danielstoller/ECE-1895-Bop-it/Enclosure/pictures/empty_enclosure_back.JPG

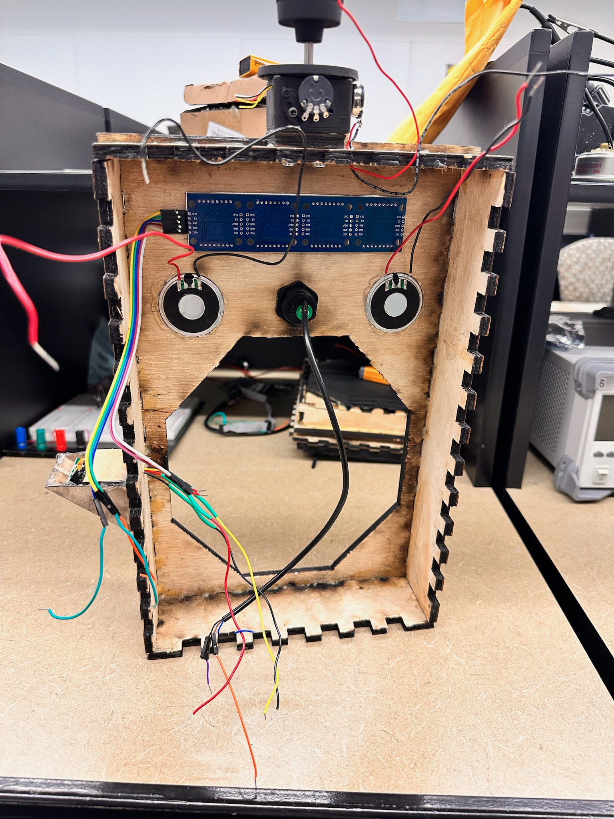
Enclosure/pictures/empty_enclosure_back.JPG
