danielstoller/ECE-1895-Bop-it/Enclosure/pictures/empty_enclosure_front.JPG

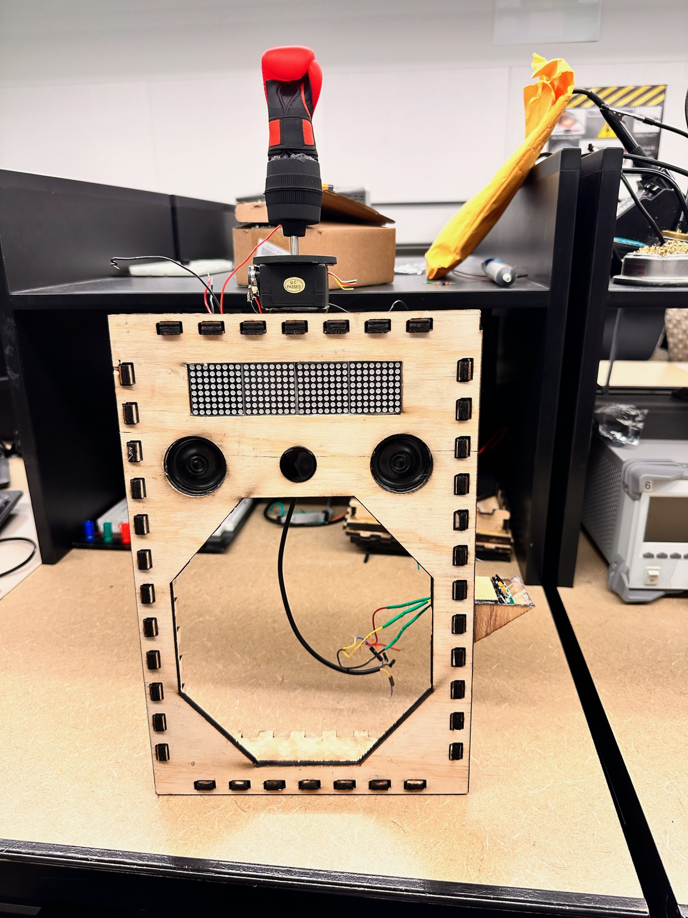
Enclosure/pictures/empty_enclosure_front.JPG
