danielstoller/ECE-1895-Bop-it/Enclosure/pictures/empty_enclosure_front_2.JPG

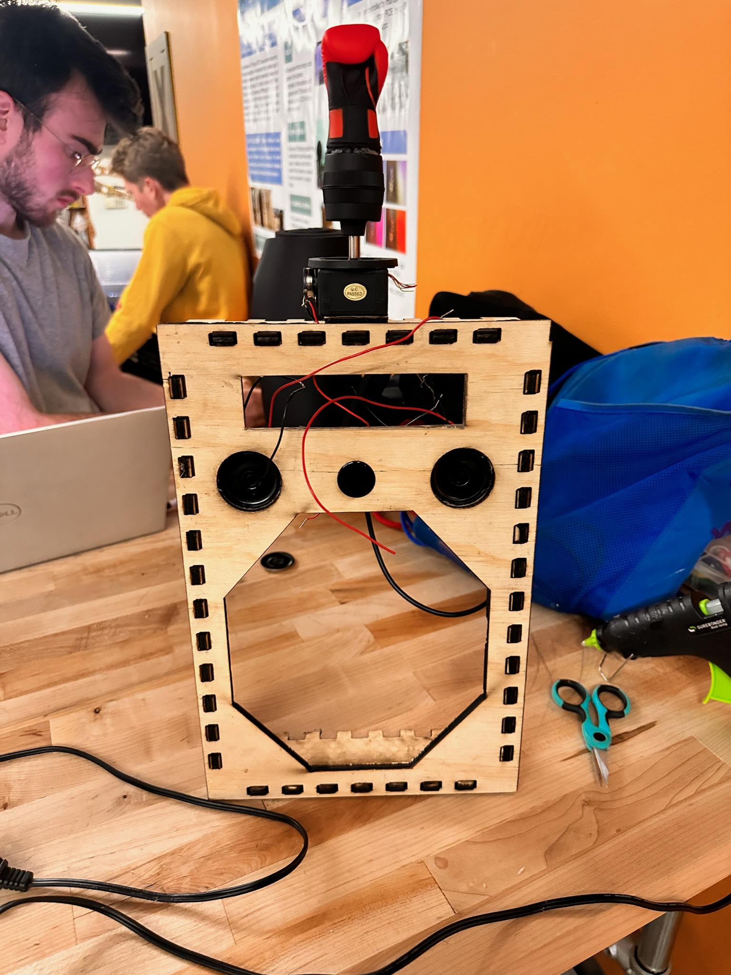
Enclosure/pictures/empty_enclosure_front_2.JPG
