danielstoller/ECE-1895-Bop-it/Enclosure/pictures/enclosure_front.JPG

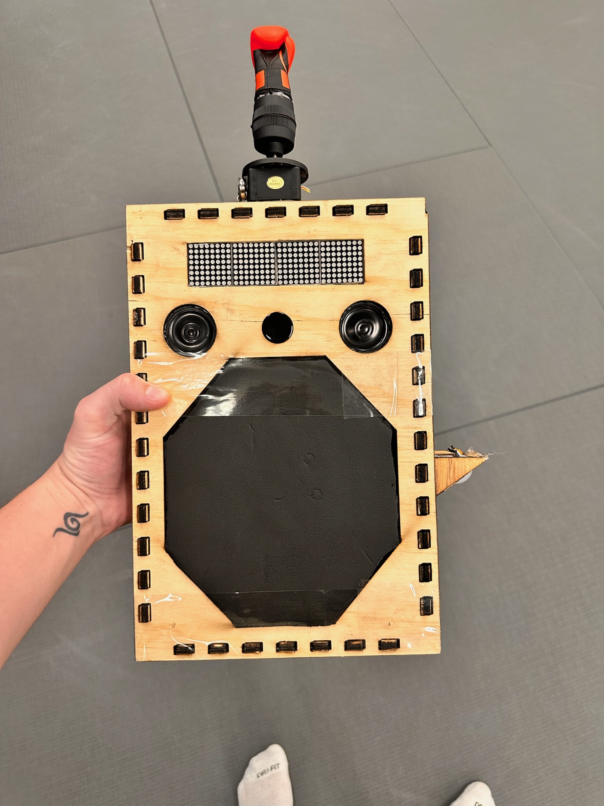
Enclosure/pictures/enclosure_front.JPG
