danielstoller/ECE-1895-Bop-it/Enclosure/pictures/enclosure_front_2.JPG

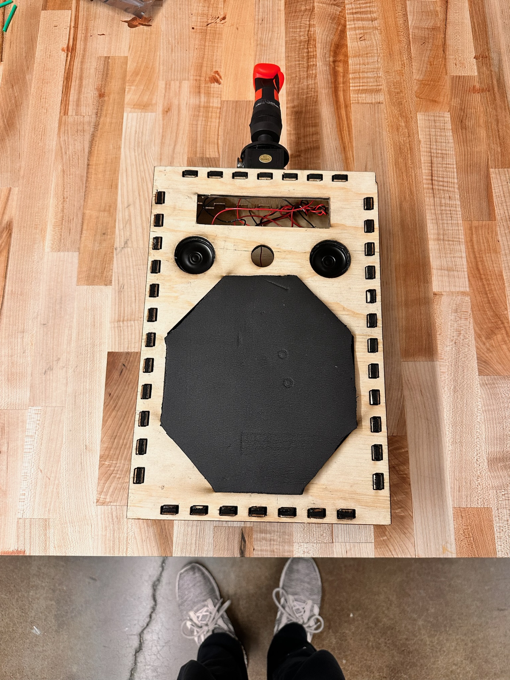
Enclosure/pictures/enclosure_front_2.JPG
