danielstoller/ECE-1895-Bop-it/Enclosure/pictures/enclosure_front_back.png

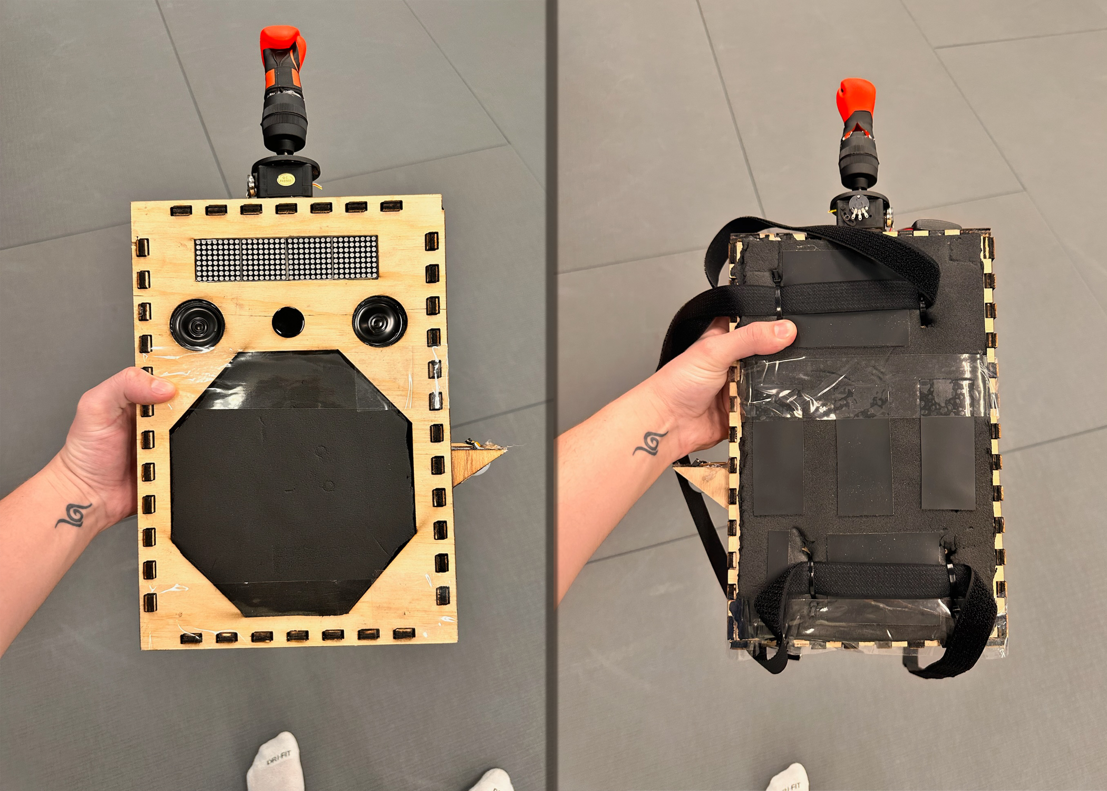
Enclosure/pictures/enclosure_front_back.png
