danielstoller/ECE-1895-Bop-it/Enclosure/pictures/enclosure_model.PNG

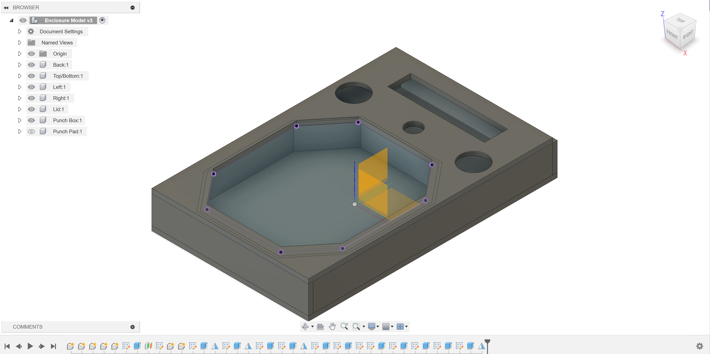
Enclosure/pictures/enclosure_model.PNG
