danielstoller/ECE-1895-Bop-it/Enclosure/pictures/enclosure_model_no_lid.PNG

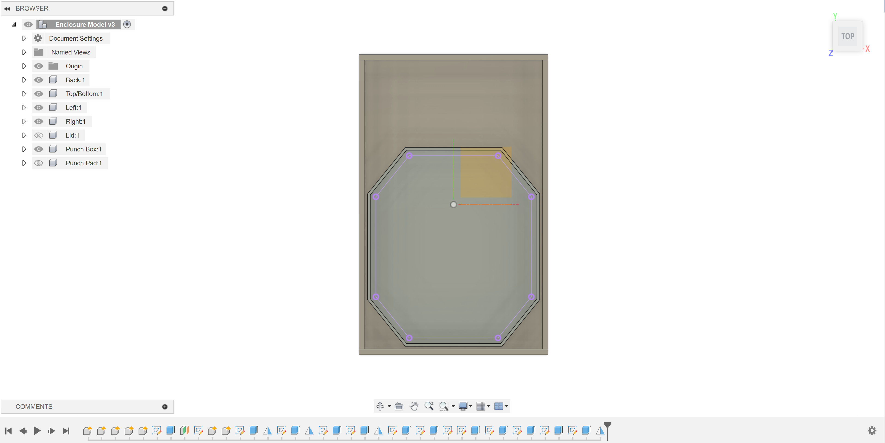
Enclosure/pictures/enclosure_model_no_lid.PNG
