danielstoller/ECE-1895-Bop-it/Enclosure/pictures/enclosure_no_lid.JPG

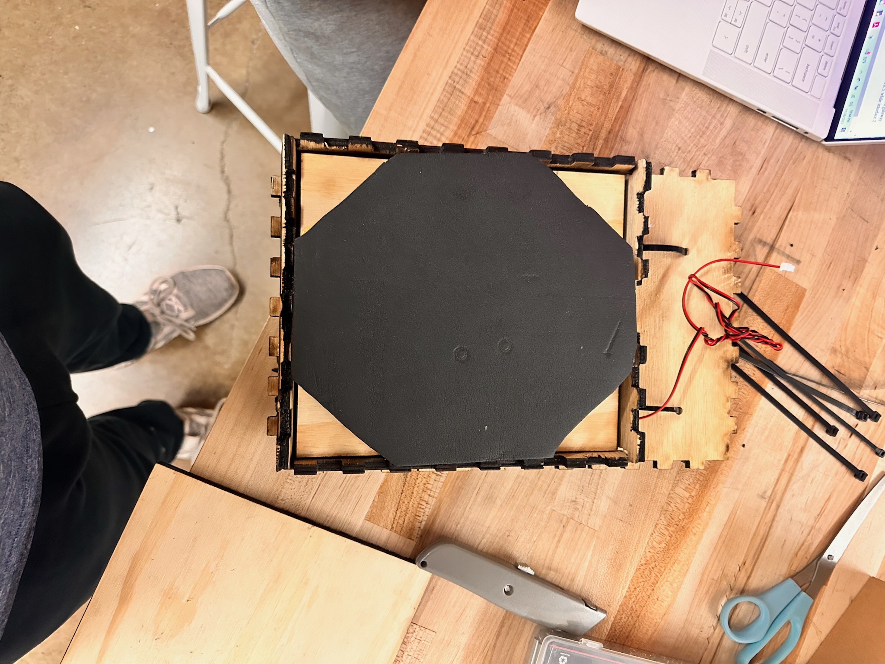
Enclosure/pictures/enclosure_no_lid.JPG
