danielstoller/ECE-1895-Bop-it/Enclosure/pictures/IMG_3901.JPG

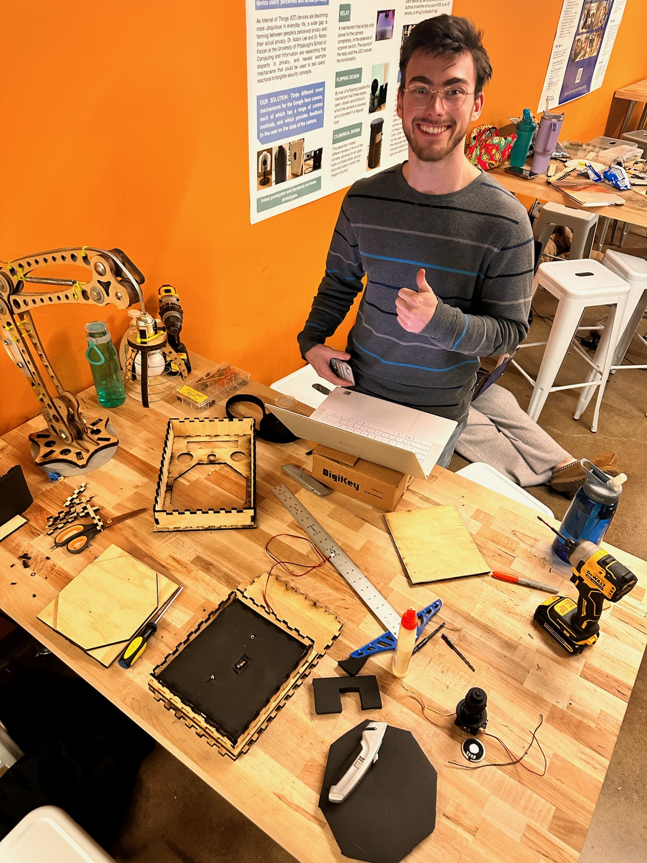
Enclosure/pictures/IMG_3901.JPG
