danielstoller/ECE-1895-Bop-it/Enclosure/pictures/separated_enclosure.JPG

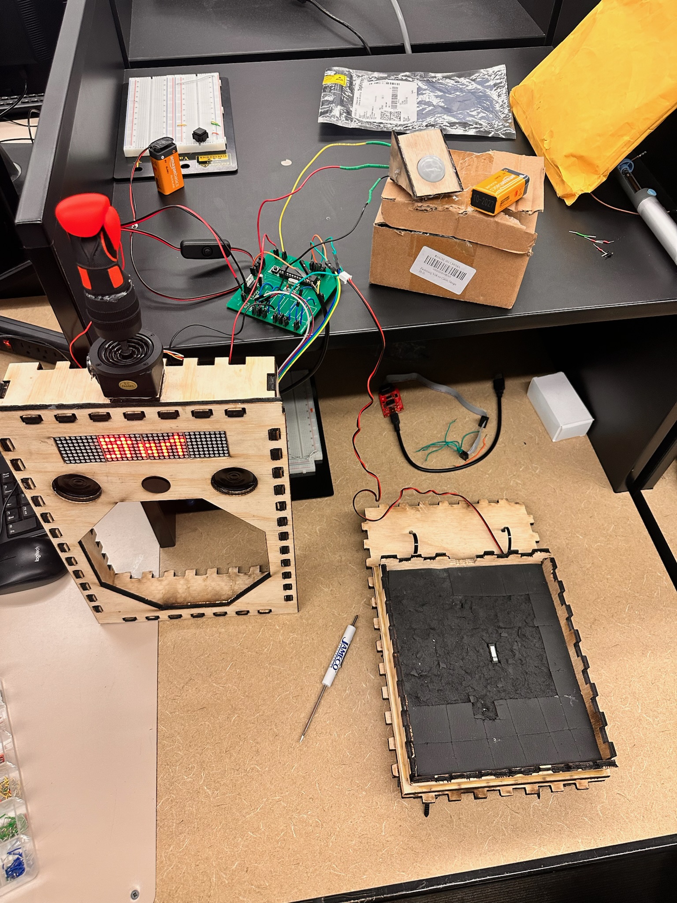
Enclosure/pictures/separated_enclosure.JPG
