danielstoller/ECE-1895-Bop-it/Pictures/IMG_3498.JPG

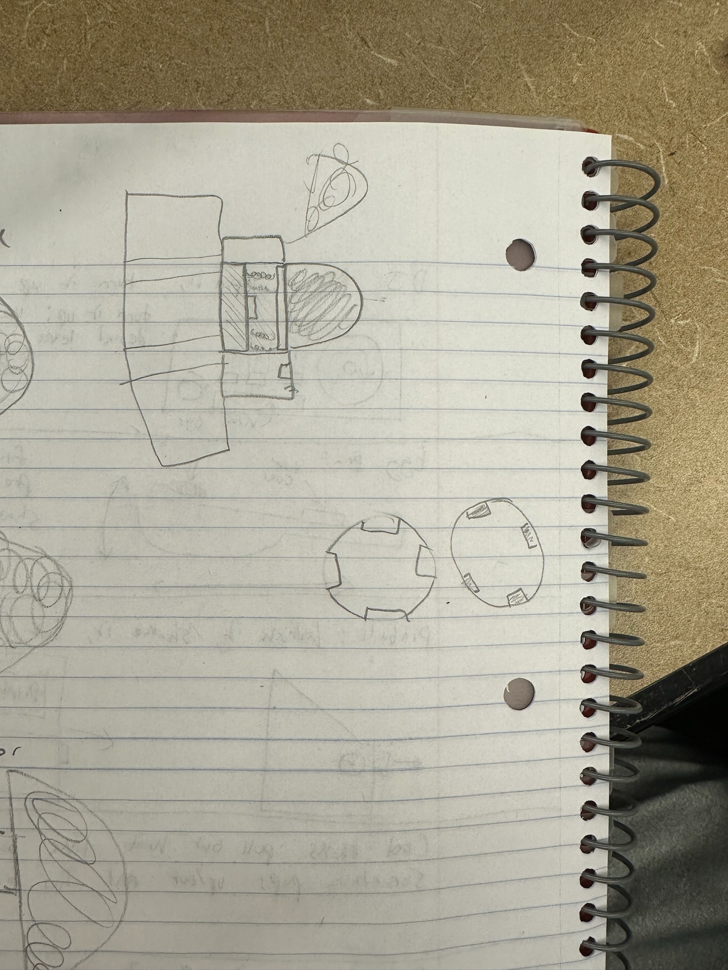
Pictures/IMG_3498.JPG
