danielstoller/ECE-1895-Bop-it/Pictures/IMG_3929.JPG

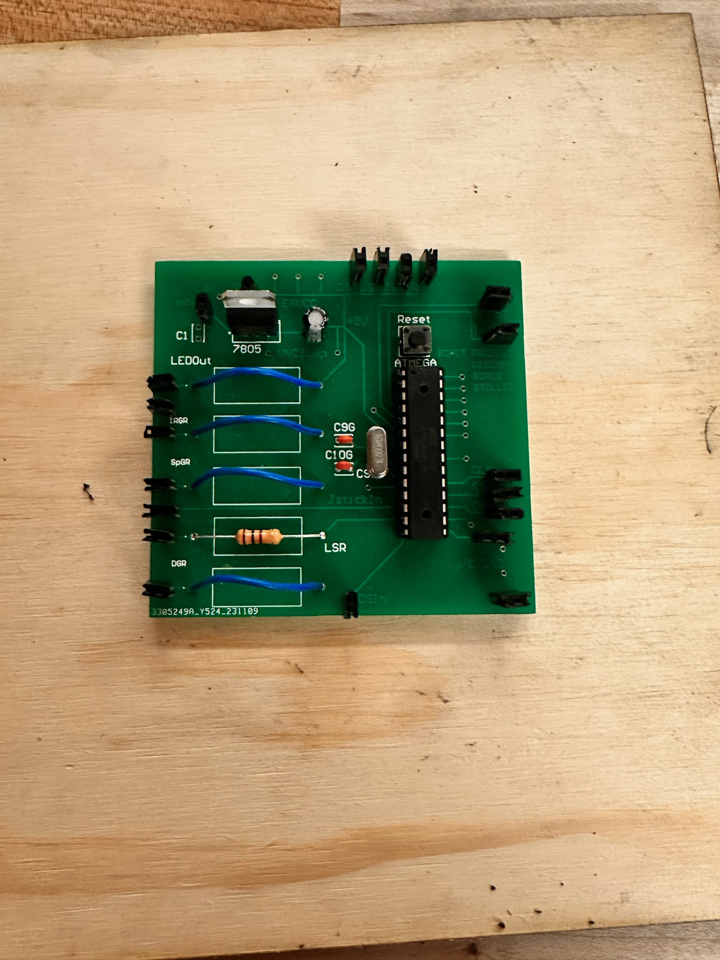
Pictures/IMG_3929.JPG
