danielstoller/ECE-1895-Bop-it/Pictures/IMG_3951.JPG

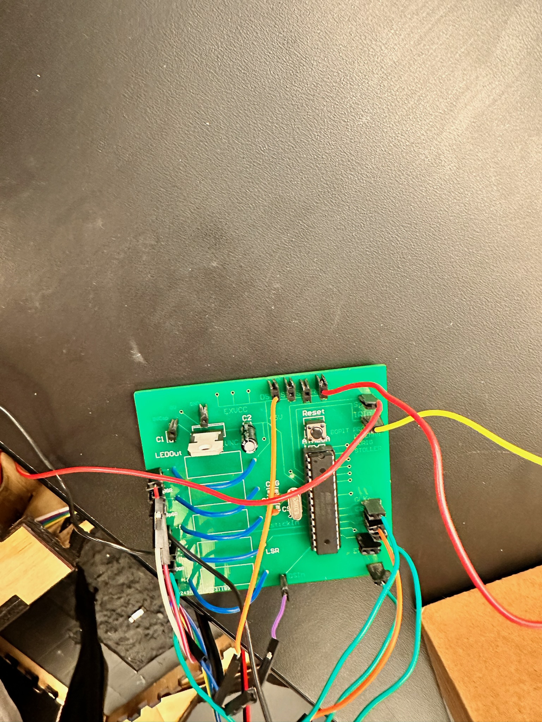
Pictures/IMG_3951.JPG
