danielstoller/ECE-1895-Bop-it/Pictures/IMG_3952.JPG

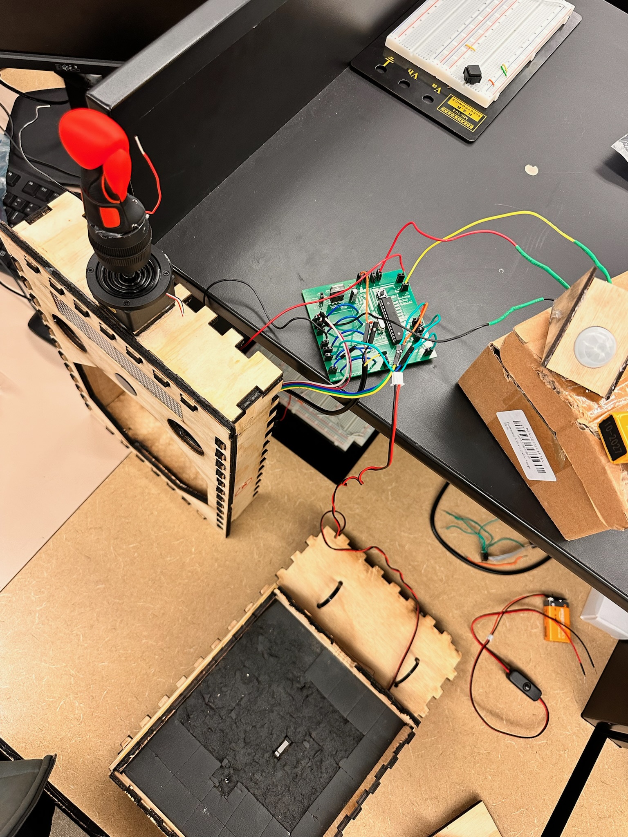
Pictures/IMG_3952.JPG
