danielstoller/ECE-1895-Bop-it/Pictures/IMG_3953.JPG

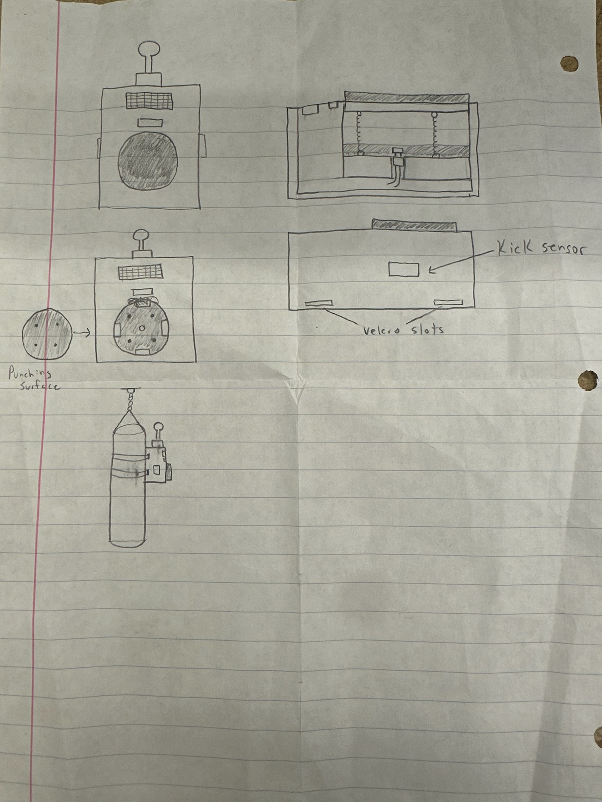
Pictures/IMG_3953.JPG
