danielstoller/ECE-1895-Bop-it/Pictures/IMG_8195.JPG

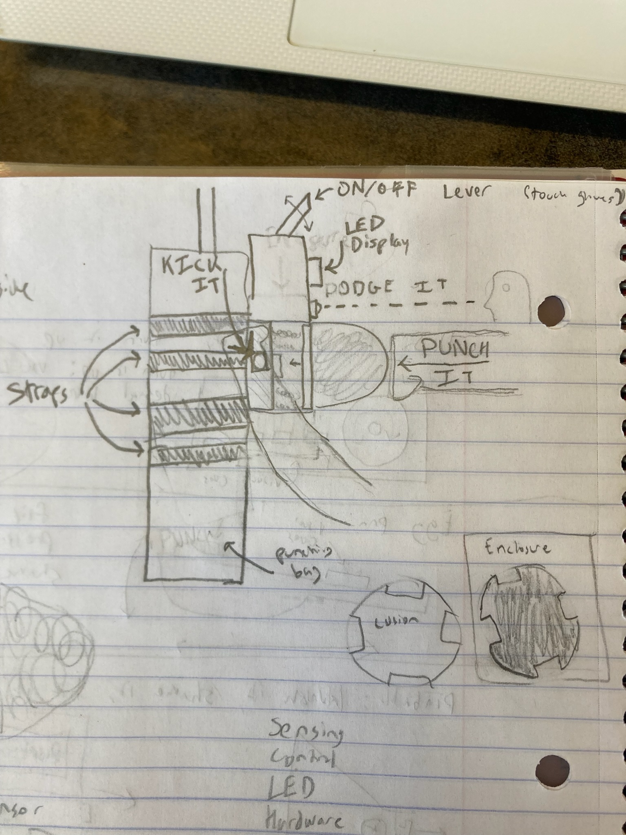
Pictures/IMG_8195.JPG
