danielstoller/ECE-1895-Bop-it/Pictures/IMG_8196.JPG

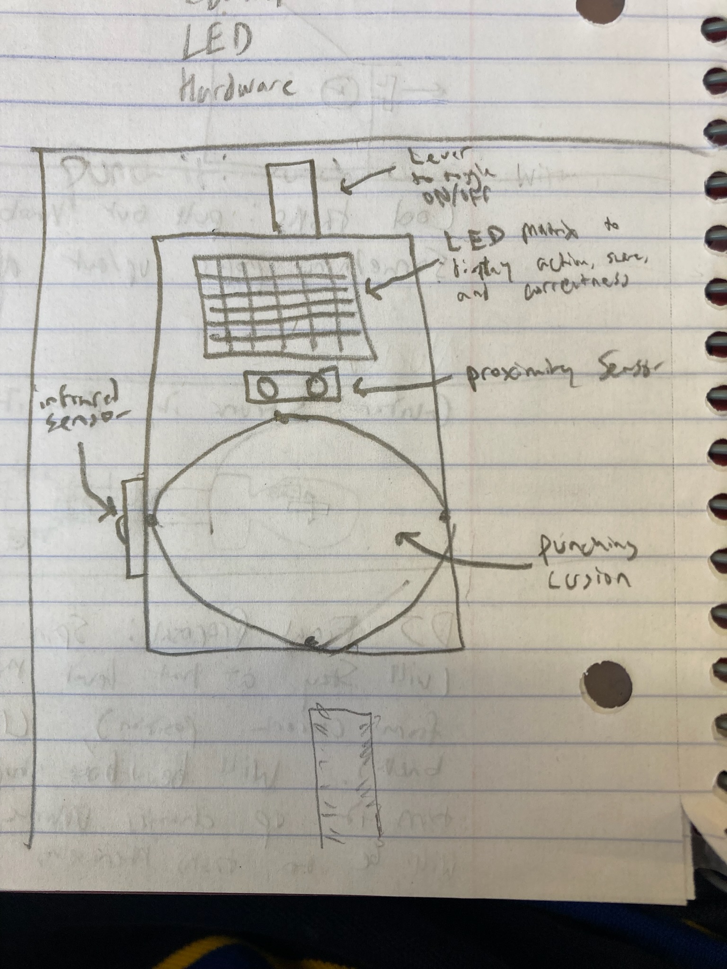
Pictures/IMG_8196.JPG
