danielstoller/ECE-1895-Bop-it/Pictures/IMG_8485.jpg

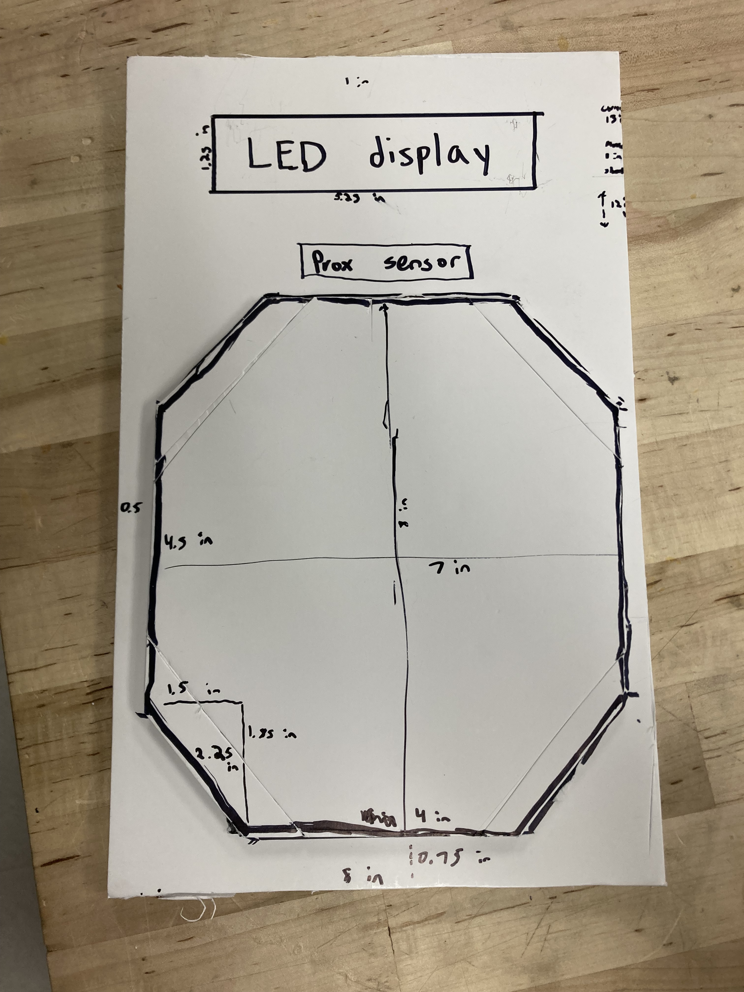
Pictures/IMG_8485.jpg
