danielstoller/ECE-1895-Bop-it/Pictures/IMG_8486.jpg

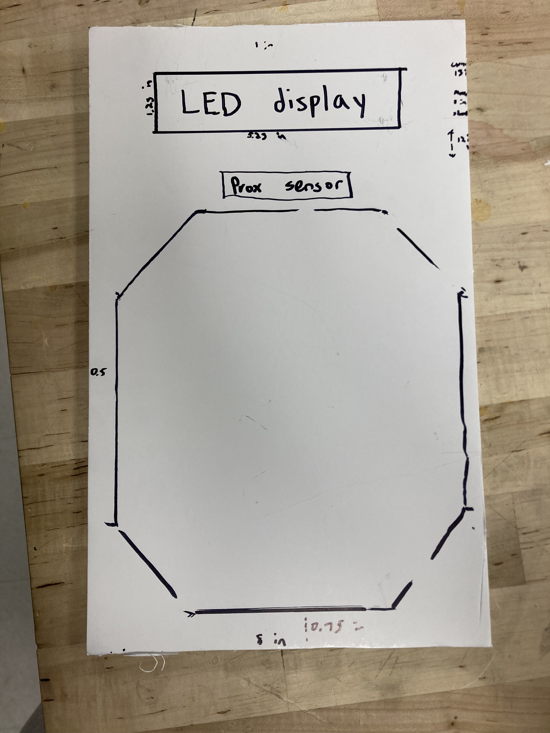
Pictures/IMG_8486.jpg
