danielstoller/ECE-1895-Bop-it/Pictures/IMG_8487.jpg

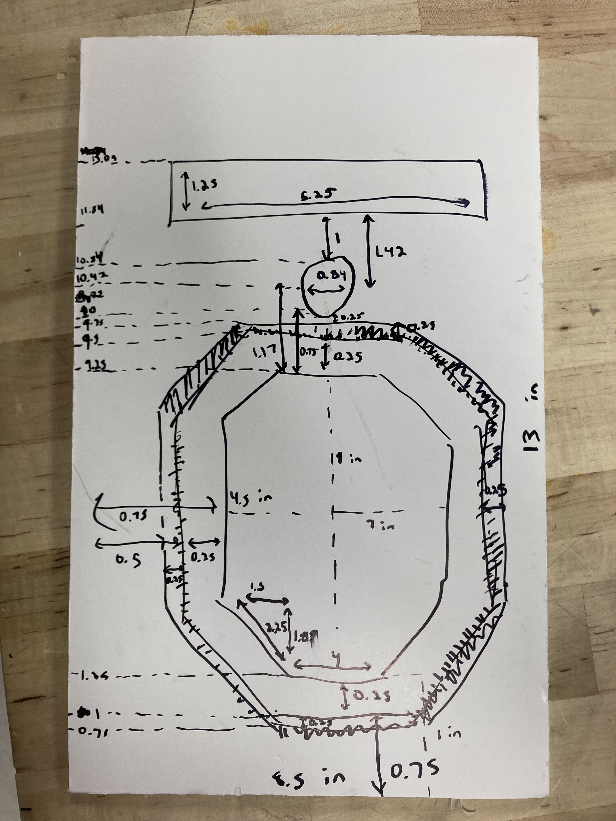
Pictures/IMG_8487.jpg
